maynej/GuepardBot/Imatges/18650_Terminals.png

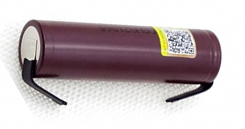
Imatges/18650_Terminals.png
