maynej/GuepardBot/Imatges/ArduinoNano.png

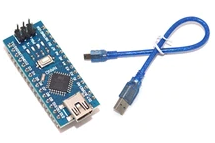
Imatges/ArduinoNano.png
