maynej/GuepardBot/Imatges/Guepard2.jpg

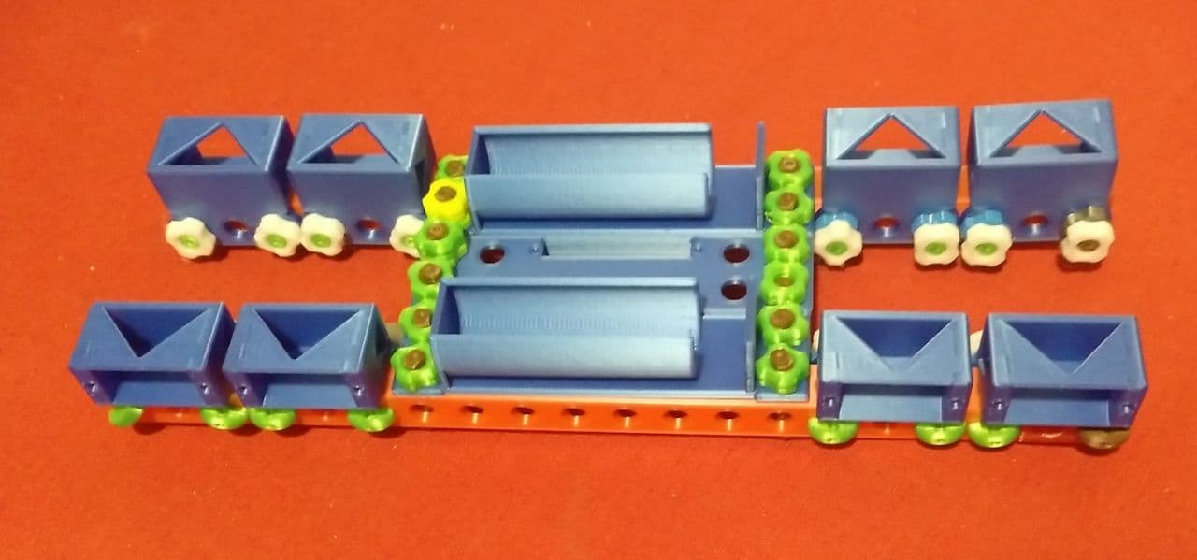
Imatges/Guepard2.jpg
