maynej/GuepardBot/Imatges/Guepard3.jpg

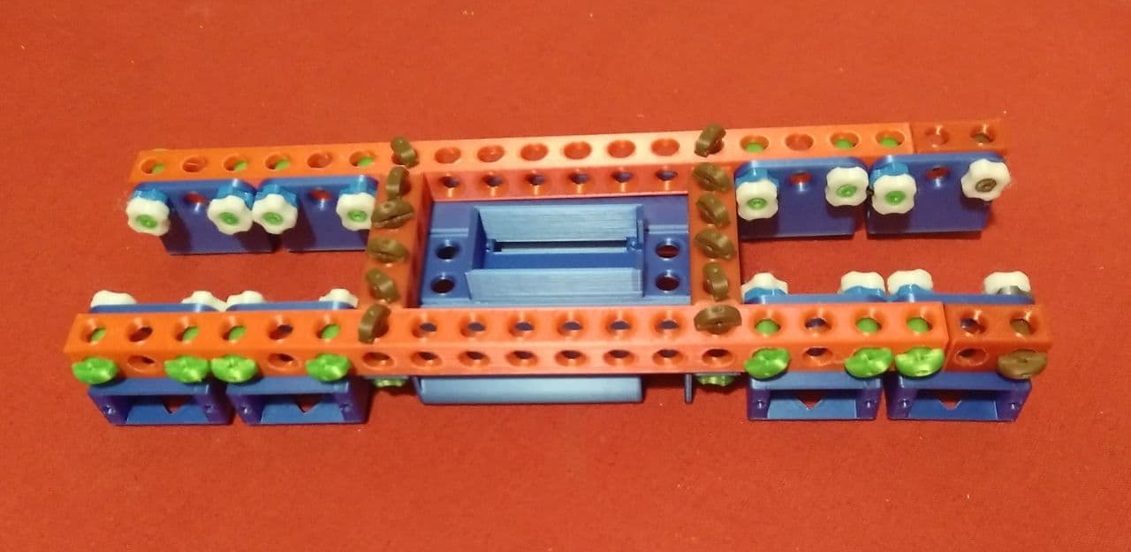
Imatges/Guepard3.jpg
