maynej/GuepardBot/Imatges/LM2956.png

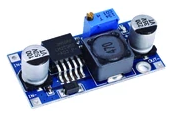
Imatges/LM2956.png
