maynej/GuepardBot/Imatges/Servo1.jpg

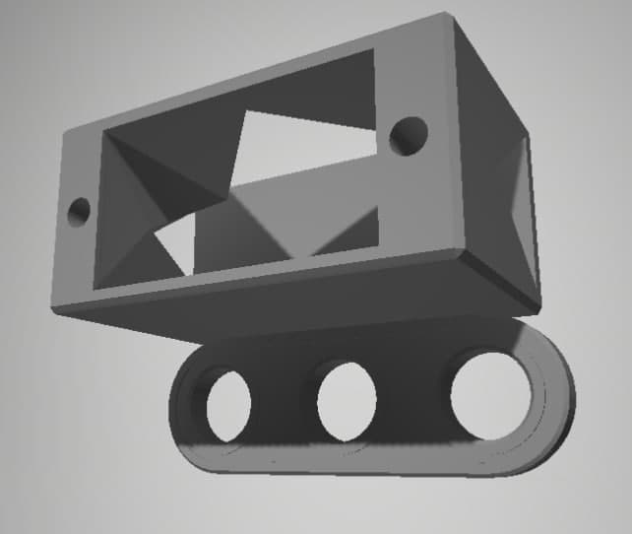
Imatges/Servo1.jpg
