maynej/GuepardBot/Imatges/ServoSG90.png

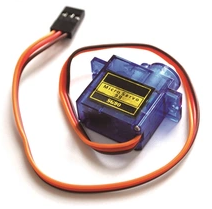
Imatges/ServoSG90.png
