maynej/GuepardBot/Imatges/SR04 vs SR04P.jpg

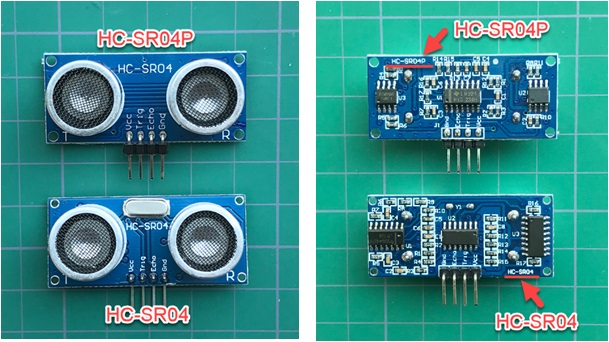
Imatges/SR04 vs SR04P.jpg
