maynej/GuepardBot/Imatges/USB_Battery18650Charger.png

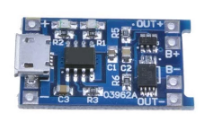
Imatges/USB_Battery18650Charger.png
