maynej/GuepardBot/STL/ShoulderScrewRHD_RH_BU00.75-SPN-SSC-0043.stl

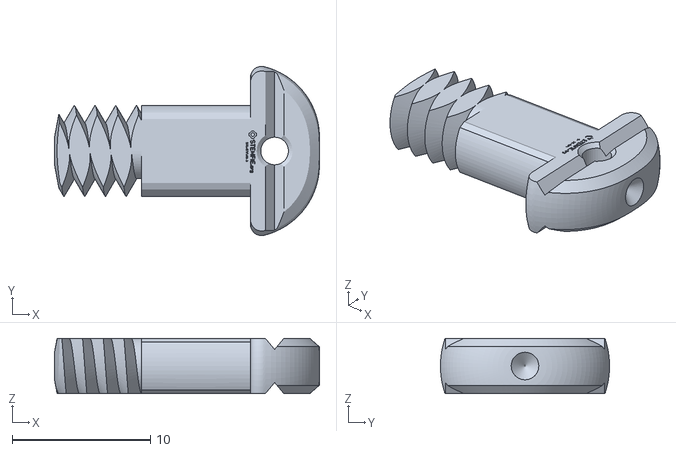
[picture p83: CAD file, 2021-03-19]
STL/ShoulderScrewRHD_RH_BU00.75-SPN-SSC-0043.stl
19.2 x 12.2 x 4.00
