maynej/GuepardBot/STL/ShoulderScrewRHD_RH_BU00.50-SPN-SSC-0042.stl

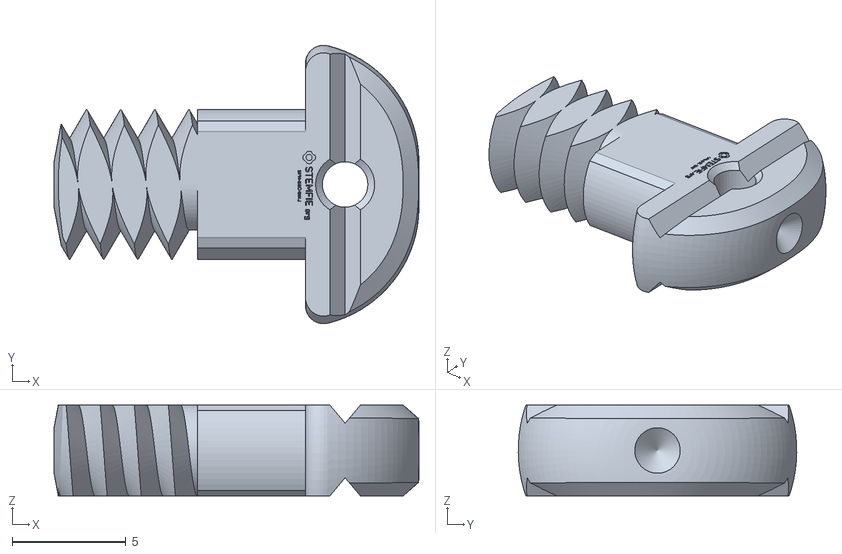
[picture p84: CAD file, 2021-03-19]
STL/ShoulderScrewRHD_RH_BU00.50-SPN-SSC-0042.stl
16.1 x 12.3 x 4.00
