maynej/GuepardBot/STL/ShoulderScrewRHD_RH_BU02.00-SPN-SSC-0048.stl

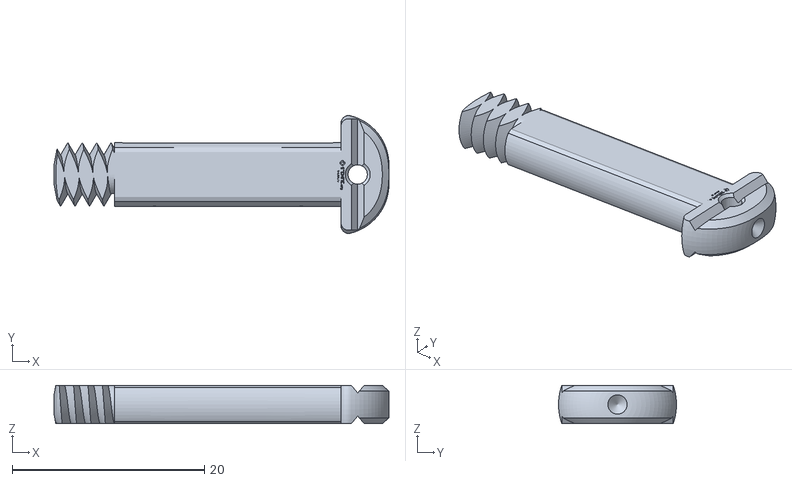
[picture p85: CAD file, 2021-03-19]
STL/ShoulderScrewRHD_RH_BU02.00-SPN-SSC-0048.stl
34.8 x 12.3 x 4.00
